mobilinkd/tk-x90-microphone-pcb/microphone.sch

## KiCad design microphone.sch (2020-07-27)

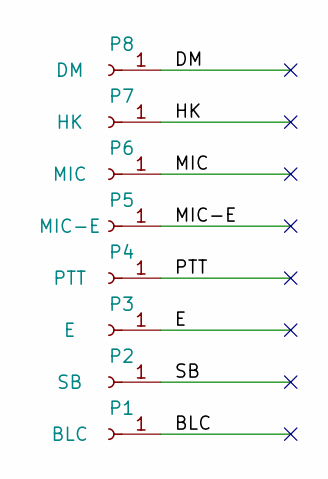
[picture p7: schematic microphone.sch]

Parts:
P1: BLC; MillMax329SolderCup
P2: SB; MillMax329SolderCup
P3: E; MillMax329SolderCup
P4: PTT; MillMax329SolderCup
P5: MIC-E; MillMax329SolderCup
P6: MIC; MillMax329SolderCup
P7: HK; MillMax329SolderCup
P8: DM; MillMax329SolderCup

Connections:
BLC: P1.1
DM: P8.1
E: P3.1
HK: P7.1
MIC: P6.1
MIC-E: P5.1
PTT: P4.1
SB: P2.1
